znoxx/UzeboxMinimal/_some_photos/mainboard.jpg

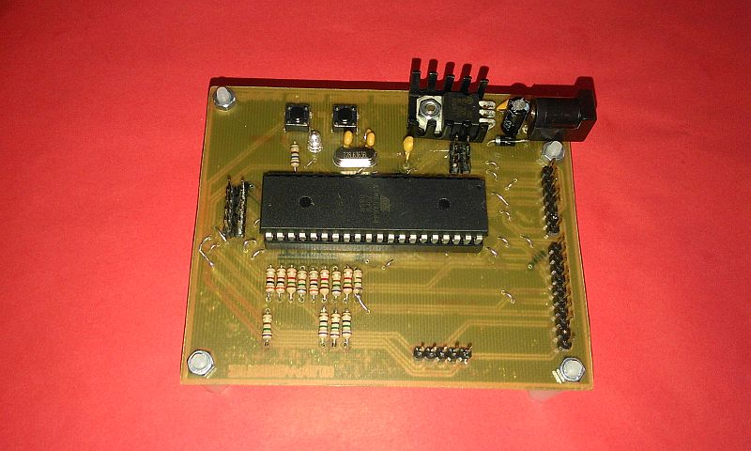
_some_photos/mainboard.jpg
