znoxx/UzeboxMinimal/_some_photos/sd_connection1.jpg

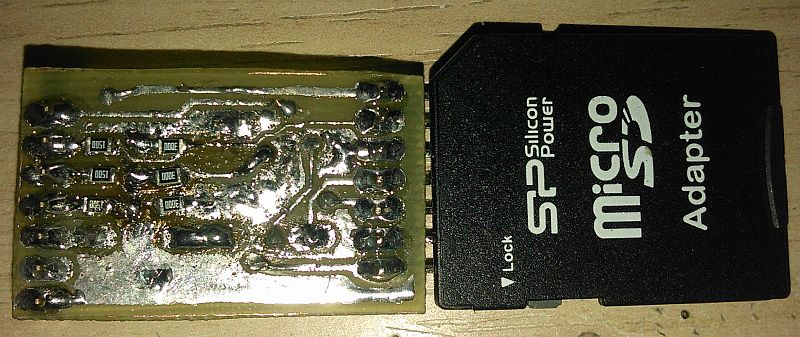
_some_photos/sd_connection1.jpg
