znoxx/UzeboxMinimal/_some_photos/video_encoder.jpg

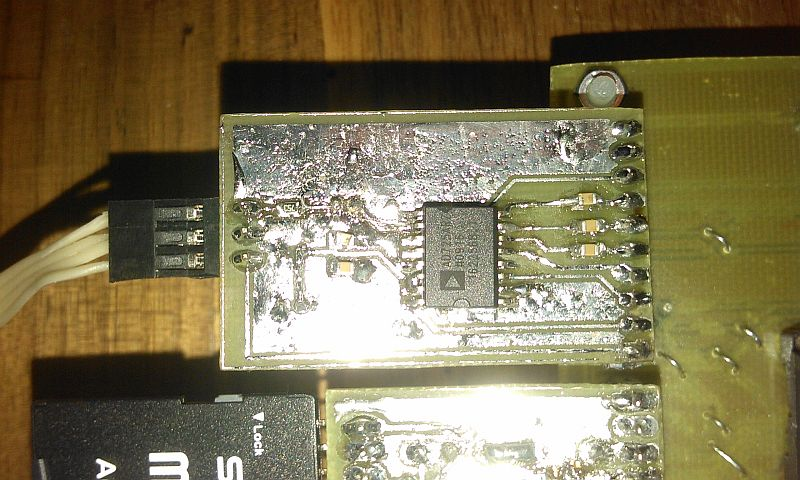
_some_photos/video_encoder.jpg
