znoxx/UzeboxMinimal/mainboard/scart/Scart.png

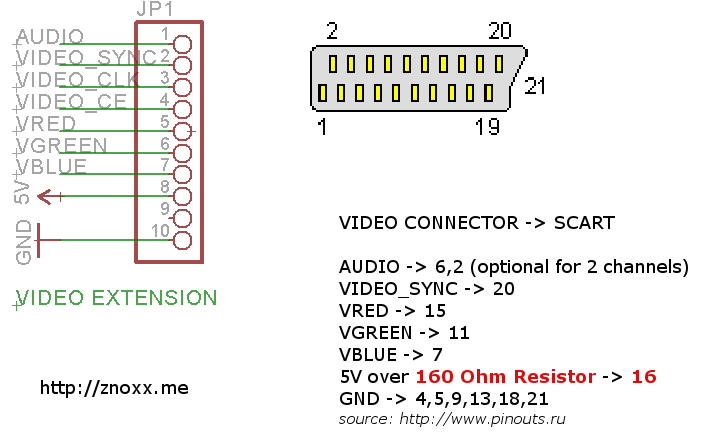
mainboard/scart/Scart.png
