znoxx/UzeboxMinimal/sdcard/schematics/top-jumpers.png

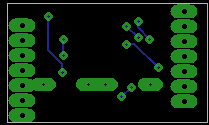
sdcard/schematics/top-jumpers.png
