znoxx/UzeboxMinimal/video-ad725/schematics/video.png

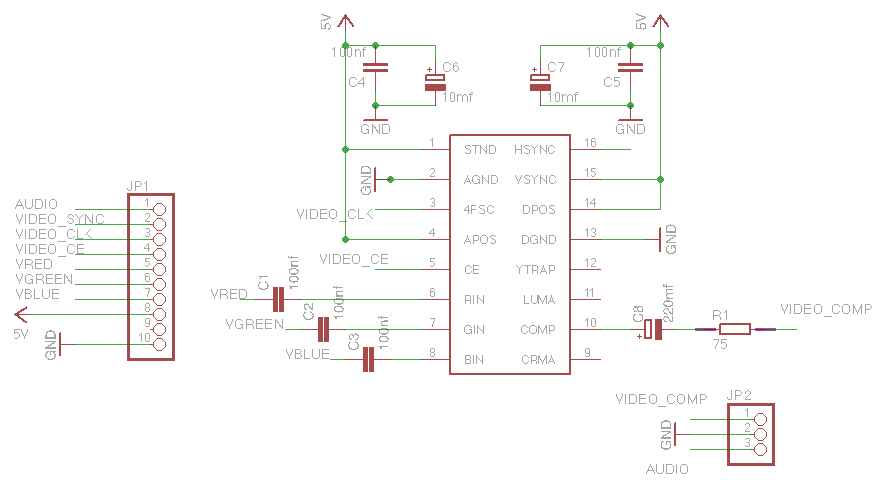
video-ad725/schematics/video.png
